GitNitneroc/PhysioPods/src/Messages.h

#ifndef MESSAGES_H
#define MESSAGES_H
#include <Arduino.h>

//This file is used to define the messages that are used to communicate between the serverpod and its clientpods
//they are parsed based on their length and then casted to the appropriate struct
namespace Messages{

    enum MessageType : uint8_t {
        ERROR,
        NOT_FOR_ME,
        LED,
        CONTROL,
        PING,
        ID_REORG,
        SSID,
        BUZZER,
    };

    /*
        *This struct is used to parse the message received from the clientpod
        *type : the type of the message
        *messageData : the data of the message
    */
    struct parsedMessage {
        MessageType type;
        void* messageData;
    };

    /*
        *This function is used to parse the message received from the clientpod
        *sender_addr : the address of the sender
        *data : the data received
        *len : the length of the data
    */
    parsedMessage getMessageType(const uint8_t * sender_addr, const uint8_t *data, int len);

    struct SSIDMessage{
        const MessageType type = MessageType::SSID;
        uint16_t sessionId;
        uint8_t ssid;

        /* SSIDMessage(uint16_t sessionId, uint8_t ssid): sessionId(sessionId), ssid(ssid){} */
    };

    /*
        *The message that is used to send the state of the LED
        *id : the id of the clientpod
        *sessionId : the session id of the pods
        *state : the state of the LED
        *mode : the mode of the LED, for different light patterns
        *r : the red value of the LED
        *g : the green value of the LED
        *b : the blue value of the LED
        *modeSpecific : some data that could be used in the specific mode
    */
    struct LEDMessage {
        const MessageType type = MessageType::LED;
        uint8_t id;
        uint16_t sessionId;
        bool state;
        uint8_t mode;
        uint8_t r;
        uint8_t g;
        uint8_t b;
        uint16_t modeSpecific;
    };

    /*
        *The message that is used to send the state of the buzzer
        *id : the id of the clientpod
        *sessionId : the session id of the pods
        *state : the state (on/off) of the buzzer
        *frequency : the frequency of the buzz sound
        *duration : the duration of the buzz sound
    */
    struct BuzzerMessage {
        const MessageType type = MessageType::BUZZER;
        uint8_t id;
        uint16_t sessionId;
        bool state; //true for on, false for off
        uint16_t frequency; //frequency in Hz
        uint16_t duration; //duration in ms
    };

    /*
        *The message that is used to send the state of the control
        *id : the id of the clientpod
        *sessionId : the session id of the pods
        *state : the state of the control
    */
    struct ControlMessage {
        const MessageType type = MessageType::CONTROL;
        uint8_t id;
        uint16_t sessionId;
        bool state; //in case we need to send a state, but for now it's only sent once on the press
    };

    struct PingMessage{ //the same struct is used for ping (client->server) and pong (server->client)
        const MessageType type = MessageType::PING;
        uint8_t id; //always the id of the client (sender for ping, destination for pong)
        uint16_t sessionId;
    };

    struct IdReorgMessage{//this is used to reorganize the ids of a pod, switch him from old to newId
        const MessageType type = MessageType::ID_REORG;
        uint8_t oldId;
        uint8_t newId;
        uint16_t sessionId;
    };
}
//constexpr size_t debugSize = sizeof(ControlMessage);

#endif //MESSAGES_H
