GitNitneroc/PhysioPods/src/handlers/LEDRequestHandler.cpp

#ifndef LEDRequestHandler_h
#define LEDRequestHandler_h
#include "ESPAsyncWebServer.h"
#include "LEDRequestHandler.h"
#include "ServerPod.h"
#include "Messages.h"
#include "debugPrint.h"
#include <esp_now.h>

LEDRequestHandler::LEDRequestHandler() {
}

bool LEDRequestHandler::canHandle(AsyncWebServerRequest *request) const {
    if (request->url()=="/LED") {
        #ifdef isDebug
        DebugPrintln("LEDRequestHandler received params: ");
        for (uint8_t i=0; i<request->params(); i++) {
            const AsyncWebParameter* p = request->getParam(i);
            DebugPrint(p->name());
            DebugPrint(": ");
            DebugPrintln(p->value());
        }
        #endif
        return true;
    }
    return false;
}

void LEDRequestHandler::handleRequest(AsyncWebServerRequest *request) {
    //this means we received a request to "/LED"
    //the parameters are always in the same ordre : LED (ON or OFF), id (the id of the pod), lightMode
    //check if the request contains a parameter "LED"
    const AsyncWebParameter* ledParam = request->getParam(0);
    bool ledState;
    uint8_t destId;
    LightMode lightMode;
    //Read the LED parameter
    if (ledParam->name()!="LED") {
        #ifdef isDebug
        DebugPrintln("LEDRequestHandler : error reading LED parameter, ignoring the request");
        #endif
        return;
    }else{
        if (ledParam->value()=="ON") {
            ledState = true;
        } else {
            ledState = false;
        }
    }
    //Read the id parameter
    const AsyncWebParameter* idParam = request->getParam(1);
    if (idParam->name()!="id") {
        #ifdef isDebug
        DebugPrintln("LEDRequestHandler : error reading id parameter, ignoring the request");
        #endif
        return;
    }else{      
        destId = idParam->value().toInt();
    }

    //Read the lightMode parameter, this one is optional and defaults to LightMode::SIMPLE
    const AsyncWebParameter* lightModeParam = request->getParam(2);
    if (lightModeParam == nullptr || lightModeParam->name()!="mode") {
        lightMode = LightMode::SIMPLE;
    }else{
        lightMode = static_cast<LightMode>(lightModeParam->value().toInt());
    }

    //let the serverPod handle the request
    ServerPod::getInstance()->setPodLightState(destId, ledState, CRGB::Teal, lightMode, 10); //10 is the modeSpecific value, only used for some mode, is arbitrary here

    //send some response to the client
    AsyncResponseStream *response = request->beginResponseStream("text/html");
    response->print("OK");
    request->send(response);
}
#endif
