GitNitneroc/PhysioPods/src/handlers/CaptiveRequestHandler.h

#include "ESPAsyncWebServer.h"
/*
    * This is a request handler for the captive portal.
*/
class CaptiveRequestHandler : public AsyncWebHandler {
public:
    CaptiveRequestHandler();
    virtual ~CaptiveRequestHandler() {}

    bool canHandle(AsyncWebServerRequest *request) const override;

    void handleRequest(AsyncWebServerRequest *request);
};
