GitNitneroc/PhysioPods/src/handlers/LEDRequestHandler.h

#include "ESPAsyncWebServer.h"

/*
 * This handles the requests to change the LED states
 * The request should be in the form of "/LED?LED=ON&id=1", the order of the parameters matters !
*/
class LEDRequestHandler : public AsyncWebHandler {
    
public:
    LEDRequestHandler();
    virtual ~LEDRequestHandler() {}

    bool canHandle(AsyncWebServerRequest *request) const override;

    void handleRequest(AsyncWebServerRequest *request);
};
