GitNitneroc/PhysioPods/src/handlers/ModeStopHandler.h

#include "ESPAsyncWebServer.h"
/*
    * This is a request handler for the captive portal.
*/
class ModeStopHandler : public AsyncWebHandler {

private:

        
public:
    ModeStopHandler();
    virtual ~ModeStopHandler() {}

    bool canHandle(AsyncWebServerRequest *request) const override;

    void handleRequest(AsyncWebServerRequest *request);
};
