GitNitneroc/PhysioPods/src/handlers/PeersNumHandler.cpp

#include "PeersNumHandler.h"
#include "ESPAsyncWebServer.h"

#ifdef ESP32
#include <WiFi.h>
#elif defined(ESP8266)
#include <ESP8266WiFi.h>
#endif

#include <esp_now.h>
#include "ServerPod.h"
#include "debugPrint.h"

PeersNumHandler::PeersNumHandler() {
}

bool PeersNumHandler::canHandle(AsyncWebServerRequest *request) const{
    if (request->url()=="/peers") {
        #ifdef isDebug
        DebugPrintln("PeersNumHandler request !");
        #endif
        return true;
    }
    return false;
}

void PeersNumHandler::handleRequest(AsyncWebServerRequest *request) {
    //start the response
    AsyncResponseStream *response = request->beginResponseStream("application/json");
    response->print("{\"peers\":");
    response->print(ServerPod::peersNum);
    response->print("}\n");

    /* DebugPrint("{\"peers\":");
    DebugPrint(ServerPod::peersNum);
    DebugPrint("}\n"); */
    //send the response
    request->send(response);
}
