GitNitneroc/PhysioPods/src/handlers/ServerMacAddressHandler.h

#include "ESPAsyncWebServer.h"
/*
    * This is a request handler for the captive portal.
*/
class ServerMacAddressHandler : public AsyncWebHandler {

private:

        
public:
    ServerMacAddressHandler();
    virtual ~ServerMacAddressHandler() {}

    bool canHandle(AsyncWebServerRequest *request);

    void handleRequest(AsyncWebServerRequest *request);
    
};
